911RSR/RaceTemp_BLE/Core/Src/stm32wbxx_it.c

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

/* Includes ------------------------------------------------------------------*/
#include "main.h"
#include "stm32wbxx_it.h"
/* USER CODE BEGIN Includes */
#include "RaceTemp.h"
/* USER CODE END Includes */

/* USER CODE BEGIN TD */
typedef struct
{
  uint32_t r0;
  uint32_t r1;
  uint32_t r2;
  uint32_t r3;
  uint32_t r12;
  uint32_t lr;
  uint32_t pc;
  uint32_t psr;
  uint32_t cfsr;
  uint32_t hfsr;
  uint32_t dfsr;
  uint32_t afsr;
  uint32_t bfar;
  uint32_t mmfar;
  uint32_t exc_return;
} RaceTemp_HardFaultDebug_t;

/* USER CODE END TD */

/* USER CODE BEGIN PV */
volatile RaceTemp_HardFaultDebug_t racetemp_hardfault_debug;
volatile uint32_t racetemp_hardfault_count;

/* USER CODE END PV */

/* USER CODE BEGIN PFP */
void RaceTemp_HardFaultCapture(uint32_t *stacked_sp, uint32_t exc_return);

/* USER CODE END PFP */

/* USER CODE BEGIN 0 */
__attribute__((used, noinline)) void RaceTemp_HardFaultCapture(uint32_t *stacked_sp, uint32_t exc_return)
{
  racetemp_hardfault_count++;

  racetemp_hardfault_debug.r0 = stacked_sp[0];
  racetemp_hardfault_debug.r1 = stacked_sp[1];
  racetemp_hardfault_debug.r2 = stacked_sp[2];
  racetemp_hardfault_debug.r3 = stacked_sp[3];
  racetemp_hardfault_debug.r12 = stacked_sp[4];
  racetemp_hardfault_debug.lr = stacked_sp[5];
  racetemp_hardfault_debug.pc = stacked_sp[6];
  racetemp_hardfault_debug.psr = stacked_sp[7];
  racetemp_hardfault_debug.cfsr = SCB->CFSR;
  racetemp_hardfault_debug.hfsr = SCB->HFSR;
  racetemp_hardfault_debug.dfsr = SCB->DFSR;
  racetemp_hardfault_debug.afsr = SCB->AFSR;
  racetemp_hardfault_debug.bfar = SCB->BFAR;
  racetemp_hardfault_debug.mmfar = SCB->MMFAR;
  racetemp_hardfault_debug.exc_return = exc_return;

  while (1)
  {
    __NOP();
  }
}

/* USER CODE END 0 */

/* External variables --------------------------------------------------------*/
extern PCD_HandleTypeDef hpcd_USB_FS;
extern DMA_HandleTypeDef hdma_adc1;
extern IPCC_HandleTypeDef hipcc;
extern RTC_HandleTypeDef hrtc;
extern DMA_HandleTypeDef hdma_usart1_rx;
extern DMA_HandleTypeDef hdma_usart1_tx;
extern UART_HandleTypeDef huart1;
/******************************************************************************/
/*           Cortex Processor Interruption and Exception Handlers          */
/******************************************************************************/
/**
  * @brief This function handles Non maskable interrupt.
  */
void NMI_Handler(void)
{
  /* USER CODE BEGIN NonMaskableInt_IRQn 1 */
   while (1)
  {
  }
  /* USER CODE END NonMaskableInt_IRQn 1 */
}

/**
  * @brief This function handles Hard fault interrupt.
  */
void HardFault_Handler(void)
{
  /* USER CODE BEGIN HardFault_IRQn 0 */
  __asm volatile
  (
    "tst lr, #4        \n"
    "ite eq            \n"
    "mrseq r0, msp     \n"
    "mrsne r0, psp     \n"
    "mov r1, lr        \n"
    "b RaceTemp_HardFaultCapture \n"
  );
  /* USER CODE END HardFault_IRQn 0 */
  while (1)
  {
  }
}

/**
  * @brief This function handles Memory management fault.
  */
void MemManage_Handler(void)
{
  while (1)
  {
  }
}

/**
  * @brief This function handles Prefetch fault, memory access fault.
  */
void BusFault_Handler(void)
{
  while (1)
  {
  }
}

/**
  * @brief This function handles Undefined instruction or illegal state.
  */
void UsageFault_Handler(void)
{
  while (1)
  {
  }
}

/**
  * @brief This function handles System service call via SWI instruction.
  */
void SVC_Handler(void)
{
}

/**
  * @brief This function handles Debug monitor.
  */
void DebugMon_Handler(void)
{
}

/**
  * @brief This function handles Pendable request for system service.
  */
void PendSV_Handler(void)
{
}

/**
  * @brief This function handles System tick timer.
  */
void SysTick_Handler(void)
{
  HAL_IncTick();
}

/******************************************************************************/
/* STM32WBxx Peripheral Interrupt Handlers                                    */
/* Add here the Interrupt Handlers for the used peripherals.                  */
/* For the available peripheral interrupt handler names,                      */
/* please refer to the startup file (startup_stm32wbxx.s).                    */
/******************************************************************************/

/**
  * @brief This function handles RTC wake-up interrupt through EXTI line 19.
  */
void RTC_WKUP_IRQHandler(void)
{
  HAL_RTCEx_WakeUpTimerIRQHandler(&hrtc);
}

/**
  * @brief This function handles DMA1 channel1 global interrupt.
  */
void DMA1_Channel1_IRQHandler(void)
{
  HAL_DMA_IRQHandler(&hdma_usart1_rx);
}

/**
  * @brief This function handles DMA1 channel2 global interrupt.
  */
void DMA1_Channel2_IRQHandler(void)
{
  HAL_DMA_IRQHandler(&hdma_usart1_tx);
}

/**
  * @brief This function handles DMA1 channel3 global interrupt.
  */
void DMA1_Channel3_IRQHandler(void)
{
  HAL_DMA_IRQHandler(&hdma_adc1);
}

/**
  * @brief This function handles USB low priority interrupt, USB wake-up interrupt through EXTI line 28.
  */
void USB_LP_IRQHandler(void)
{
  HAL_PCD_IRQHandler(&hpcd_USB_FS);
}

/**
  * @brief This function handles TIM2 global interrupt.
  */
void TIM2_IRQHandler(void)
{
  /* USER CODE BEGIN TIM2_IRQn 0 */
	if (LL_TIM_IsActiveFlag_CC1(TIM2))
	{
		uint32_t capture = LL_TIM_IC_GetCaptureCH1(TIM2);

		LL_TIM_ClearFlag_CC1(TIM2);
		LL_TIM_ClearFlag_CC1OVR(TIM2);
		RaceTemp_ignition_pulse_isr(capture);
	}

	if (LL_TIM_IsActiveFlag_CC1OVR(TIM2))
	{
		LL_TIM_ClearFlag_CC1OVR(TIM2);
	}

	if (LL_TIM_IsActiveFlag_UPDATE(TIM2))
	{
		LL_TIM_ClearFlag_UPDATE(TIM2);
	}

  /* USER CODE END TIM2_IRQn 0 */
}

/**
  * @brief This function handles USART1 global interrupt.
  */
void USART1_IRQHandler(void)
{
  HAL_UART_IRQHandler(&huart1);
}

/**
  * @brief This function handles IPCC RX occupied interrupt.
  */
void IPCC_C1_RX_IRQHandler(void)
{
  HAL_IPCC_RX_IRQHandler(&hipcc);
}

/**
  * @brief This function handles IPCC TX free interrupt.
  */
void IPCC_C1_TX_IRQHandler(void)
{
  HAL_IPCC_TX_IRQHandler(&hipcc);
}

/**
  * @brief This function handles HSEM global interrupt.
  */
void HSEM_IRQHandler(void)
{
  HAL_HSEM_IRQHandler();
}

/**
  * @brief This function handles DMAMUX1 overrun interrupt.
  */
void DMAMUX1_OVR_IRQHandler(void)
{
  // Handle DMA1_Channel3
  HAL_DMAEx_MUX_IRQHandler(&hdma_adc1);
}
